Verksmidja/V23_Agust_Ragnar_RagnarAgust/Laser_Tag_3d/Laser_Tag_gun_shell_4207521/images/featured_preview_20200212_155145_2.jpg

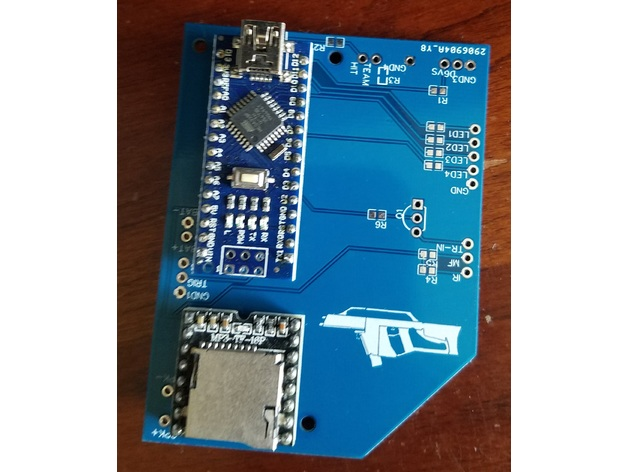
Laser_Tag_3d/Laser_Tag_gun_shell_4207521/images/featured_preview_20200212_155145_2.jpg
