Verksmidja/V23_Agust_Ragnar_RagnarAgust/Laser_Tag_3d/Laser_Tag_gun_shell_4207521/images/LT_Ammo_count.png

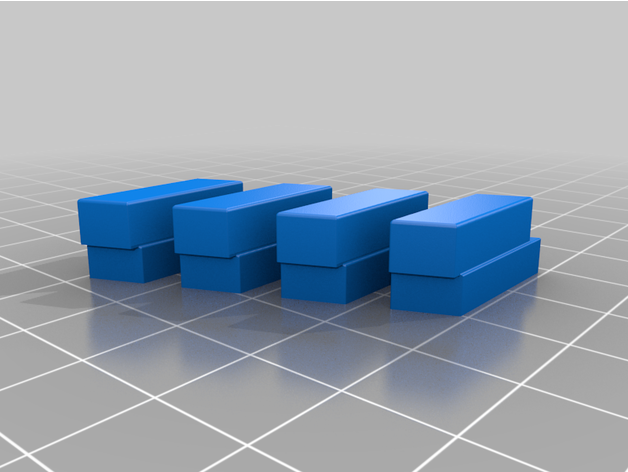
Laser_Tag_3d/Laser_Tag_gun_shell_4207521/images/LT_Ammo_count.png
