Verksmidja/V23_Agust_Ragnar_RagnarAgust/Laser_Tag_3d/Laser_Tag_gun_shell_4207521/images/Right_LT_base.png

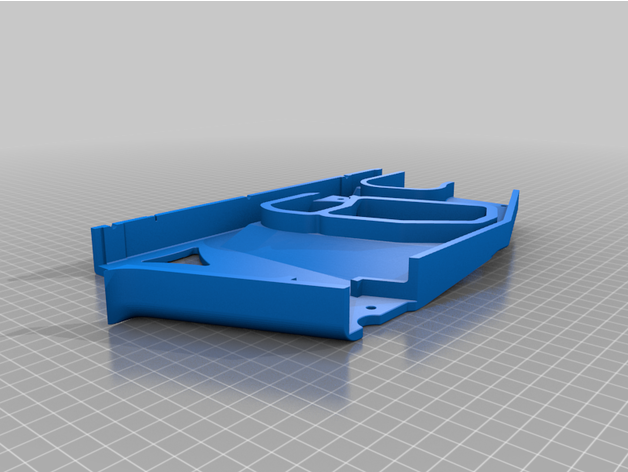
Laser_Tag_3d/Laser_Tag_gun_shell_4207521/images/Right_LT_base.png
